dsaltas/WiFi-WebRadio/Doc/bottom_rendered.png

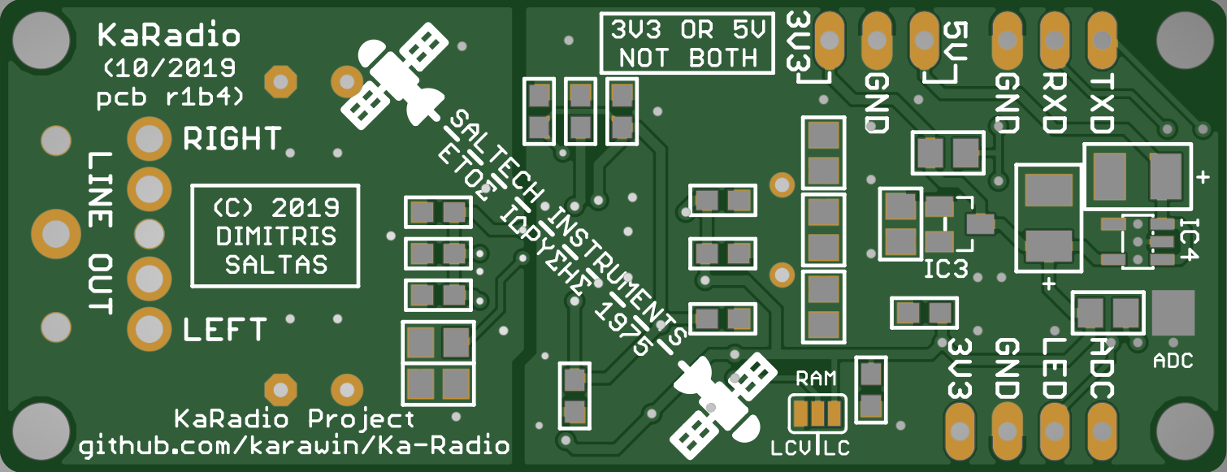
Doc/bottom_rendered.png
